s-grundner/CTN-HexGauge/source/LCD_Module_RPI_code/RaspberryPi/c/examples/LCD_1in3_test.c

#include "DEV_Config.h"
#include "LCD_1in3.h"
#include "GUI_Paint.h"
#include "GUI_BMP.h"
#include "test.h"
#include <stdio.h>  //printf()
#include <stdlib.h> //exit()
#include <signal.h> //signal()

void LCD_1IN3_test(void)
{
    // Exception handling:ctrl + c
    signal(SIGINT, Handler_1IN3_LCD);

    /* Module Init */
    if (DEV_ModuleInit() != 0)
    {
        DEV_ModuleExit();
        exit(0);
    }

    /* LCD Init */
    printf("1.3inch LCD demo...\r\n");
    LCD_1IN3_Init(HORIZONTAL);
    LCD_1IN3_Clear(WHITE);
    // LCD_SetBacklight(1023);

    UWORD *BlackImage;
    UDOUBLE Imagesize = LCD_1IN3_HEIGHT * LCD_1IN3_WIDTH * 2;
    printf("Imagesize = %d\r\n", Imagesize);
    if ((BlackImage = (UWORD *)malloc(Imagesize)) == NULL)
    {
        printf("Failed to apply for black memory...\r\n");
        exit(0);
    }
    // /*1.Create a new image cache named IMAGE_RGB and fill it with white*/
    Paint_NewImage(BlackImage, LCD_1IN3_WIDTH, LCD_1IN3_HEIGHT, 0, WHITE, 16);
    Paint_Clear(WHITE);
    Paint_SetRotate(ROTATE_90);
    // /* GUI */
    printf("drawing...\r\n");
    // /*2.Drawing on the image*/
    Paint_DrawPoint(5, 10, BLACK, DOT_PIXEL_1X1, DOT_STYLE_DFT); // 240 240
    Paint_DrawPoint(5, 25, BLACK, DOT_PIXEL_2X2, DOT_STYLE_DFT);
    Paint_DrawPoint(5, 40, BLACK, DOT_PIXEL_3X3, DOT_STYLE_DFT);
    Paint_DrawPoint(5, 55, BLACK, DOT_PIXEL_4X4, DOT_STYLE_DFT);

    Paint_DrawLine(20, 10, 70, 60, RED, DOT_PIXEL_1X1, LINE_STYLE_SOLID);
    Paint_DrawLine(70, 10, 20, 60, RED, DOT_PIXEL_1X1, LINE_STYLE_SOLID);
    Paint_DrawLine(170, 15, 170, 55, RED, DOT_PIXEL_1X1, LINE_STYLE_DOTTED);
    Paint_DrawLine(150, 35, 190, 35, RED, DOT_PIXEL_1X1, LINE_STYLE_DOTTED);

    Paint_DrawRectangle(20, 10, 70, 60, BLUE, DOT_PIXEL_1X1, DRAW_FILL_EMPTY);
    Paint_DrawRectangle(85, 10, 130, 60, BLUE, DOT_PIXEL_1X1, DRAW_FILL_FULL);

    Paint_DrawCircle(170, 35, 20, GREEN, DOT_PIXEL_1X1, DRAW_FILL_EMPTY);
    Paint_DrawCircle(170, 85, 20, GREEN, DOT_PIXEL_1X1, DRAW_FILL_FULL);

    Paint_DrawString_EN(5, 70, "hello world", &Font16, WHITE, BLACK);
    Paint_DrawString_EN(5, 90, "waveshare", &Font20, RED, IMAGE_BACKGROUND);

    Paint_DrawNum(5, 160, 123456789, &Font20, GREEN, IMAGE_BACKGROUND);
    Paint_DrawString_CN(5, 200, "΢ѩ����", &Font24CN, IMAGE_BACKGROUND, BLUE);

    // /*3.Refresh the picture in RAM to LCD*/
    LCD_1IN3_Display(BlackImage);
    DEV_Delay_ms(2000);

    // /* show bmp */
    printf("show bmp\r\n");
    GUI_ReadBmp("./pic/LCD_1inch3.bmp");

    LCD_1IN3_Display(BlackImage);
    DEV_Delay_ms(2000);

    /* Module Exit */
    free(BlackImage);
    BlackImage = NULL;
    DEV_ModuleExit();
}
